andress7002/SeniorDesign/PCB Design/KiCad/CurrentSensing_DAUGHTERBOARD.kicad_sch

## KiCad design PCB Design/KiCad/CurrentSensing_DAUGHTERBOARD.kicad_sch (2026-03-03)

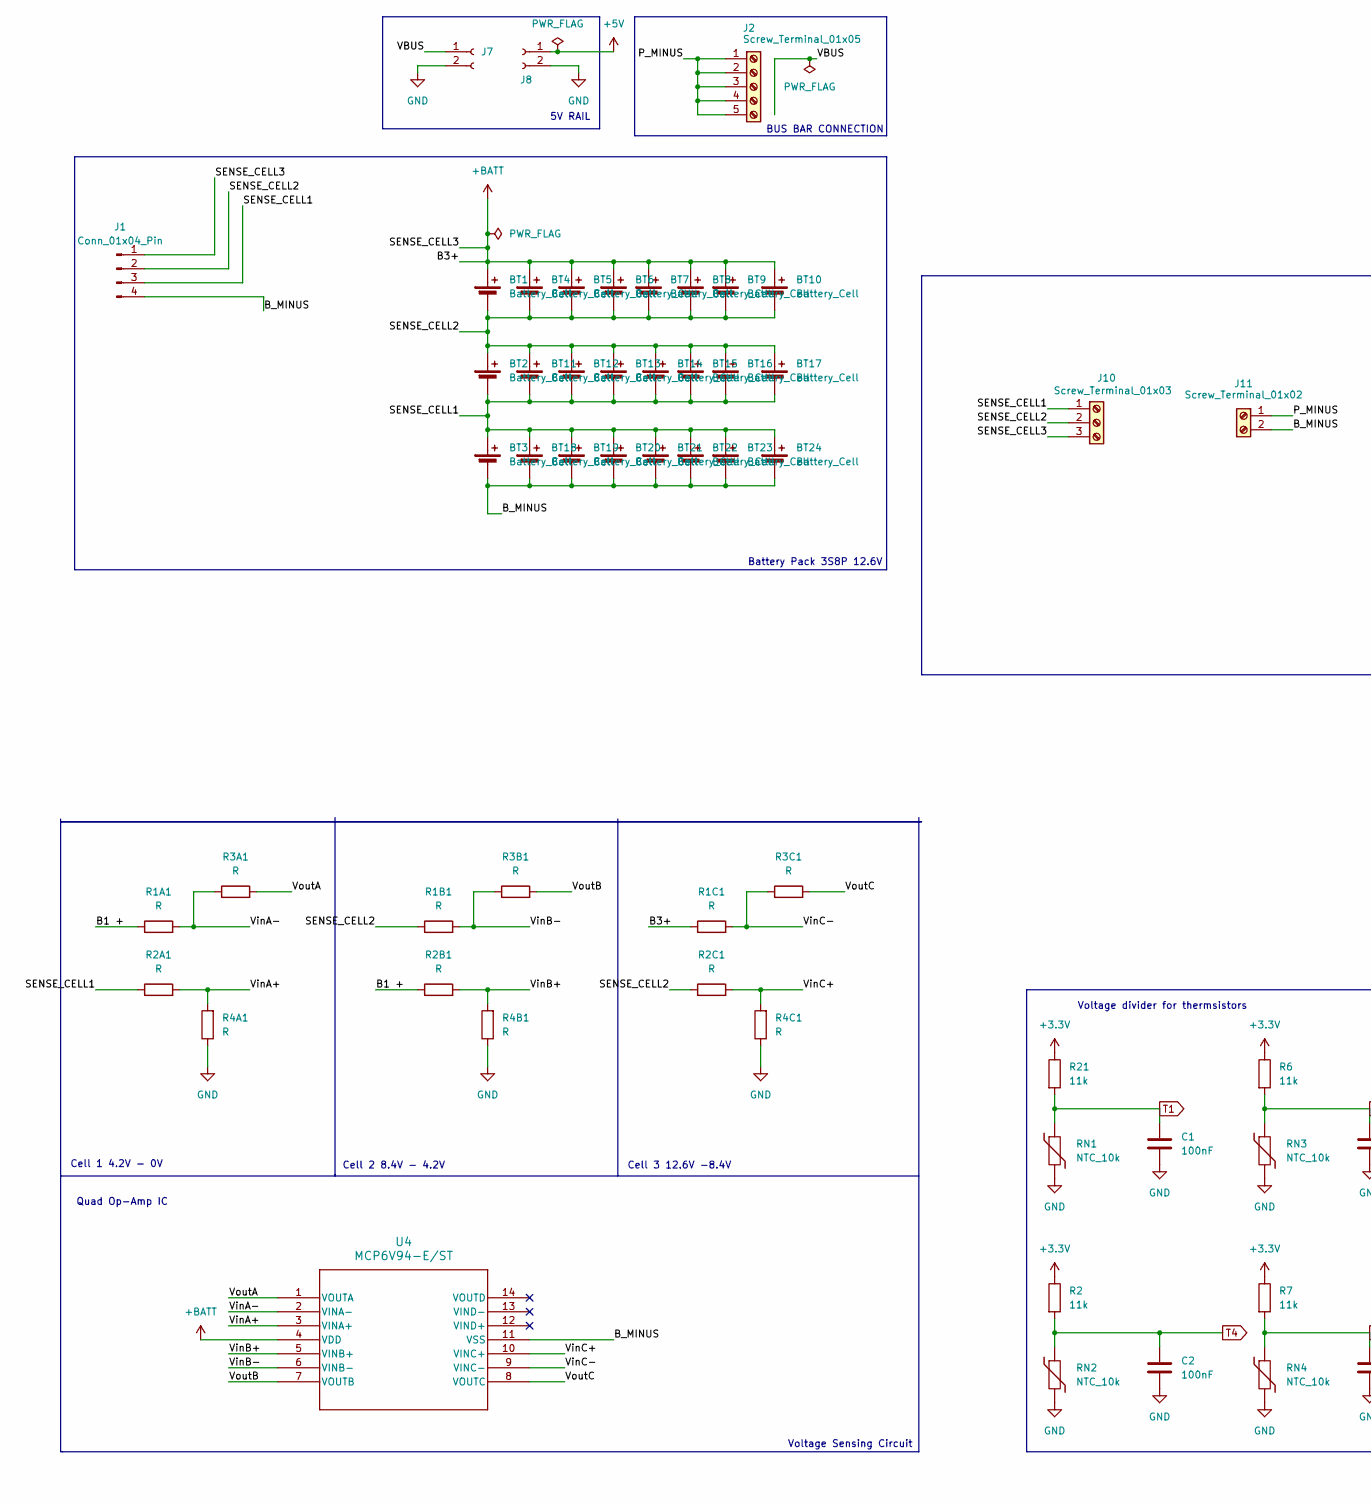
[picture p2: schematic CurrentSensing_DAUGHTERBOARD.kicad_sch, part in row 1, column 1]

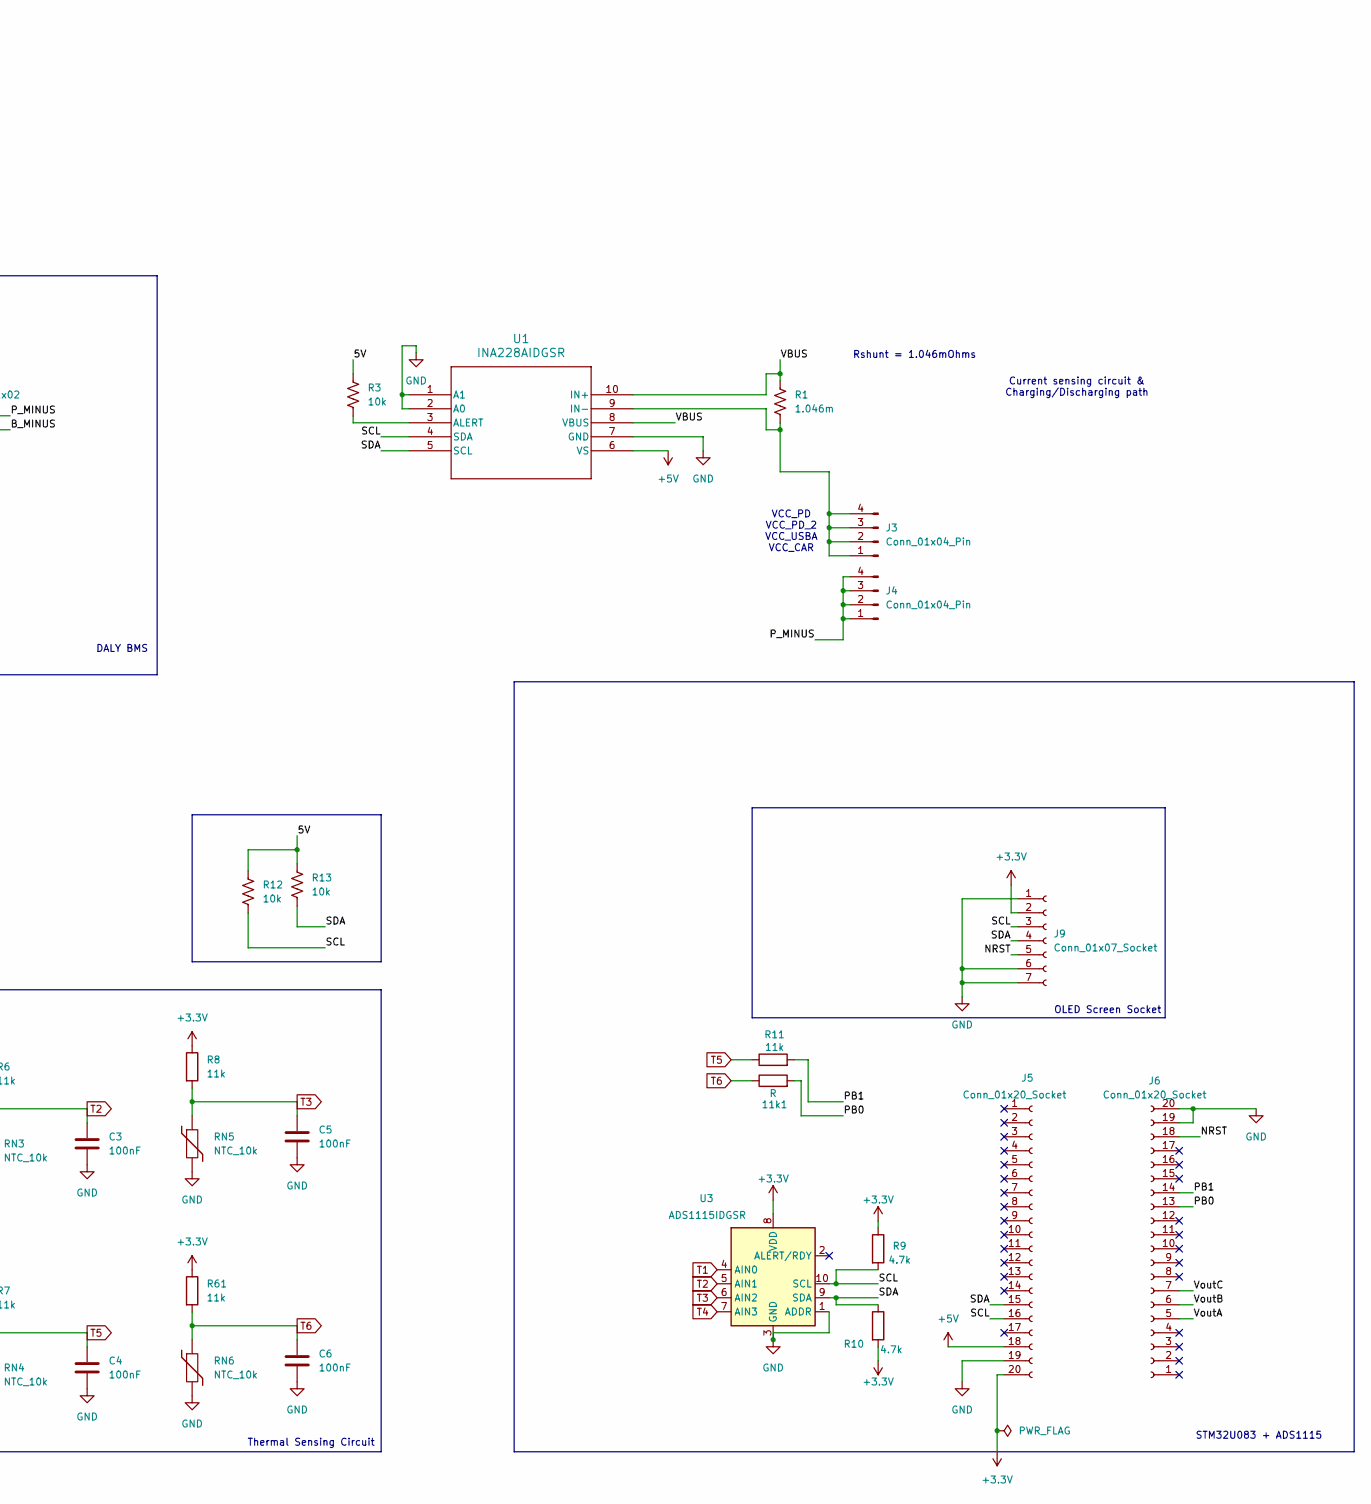
[picture p3: schematic CurrentSensing_DAUGHTERBOARD.kicad_sch, part in row 1, column 2]

Parts:
11k1: R
BT1, BT2, BT3, BT4, BT5, BT6, BT7, BT8, BT9, BT10, BT11, BT12, BT13, BT14, BT15, BT16, BT17, BT18, BT19, BT20, BT21, BT22, BT23, BT24: Battery_Cell
C1, C2, C3, C4, C5, C6: 100nF
J1, J3, J4: Conn_01x04_Pin
J2: Screw_Terminal_01x05
J5, J6: Conn_01x20_Socket
J7, J8: Conn_01x02_Socket
J9: Conn_01x07_Socket
J10: Screw_Terminal_01x03
J11: Screw_Terminal_01x02
R1: 1.046m
R1A1, R1B1, R1C1, R2A1, R2B1, R2C1, R3A1, R3B1, R3C1, R4A1, R4B1, R4C1: R
R2, R6, R7, R8, R11, R21, R61: 11k
R3, R12, R13: 10k
R9, R10: 4.7k
RN1, RN2, RN3, RN4, RN5, RN6: NTC_10k
U1: INA228AIDGSR; VSSOP10_DGS_TEX
U3: ADS1115IDGSR; MSOP-10_3x3mm_P0.5mm
U4: MCP6V94-E/ST; TSSOP14_ST_MCH

Connections:
5V: R3.1, R12.1, R13.1
+3.3V: J5.20, J9.2, R2.1, R6.1, R7.1, R8.1, R9.1, R10.2, R21.1, R61.1, U3.8 (VDD)
+5V: J5.18, J8.1, U1.6 (VS)
+BATT: BT1.1 (+), BT4.1 (+), BT5.1 (+), BT6.1 (+), BT7.1 (+), BT8.1 (+), BT9.1 (+), BT10.1 (+), J1.1, J10.3, R1C1.1, U4.4 (VDD)
B1 +: R1A1.1, R2B1.1
B_MINUS: BT3.2 (-), BT18.2 (-), BT19.2 (-), BT20.2 (-), BT21.2 (-), BT22.2 (-), BT23.2 (-), BT24.2 (-), J1.4, J11.2, U4.11 (VSS)
GND: C1.2, C2.2, C3.2, C4.2, C5.2, C6.2, J5.19, J6.19, J6.20, J7.2, J8.2, J9.1, J9.6, J9.7, R4A1.1, R4B1.1, R4C1.1, RN1.2, RN2.2, RN3.2, RN4.2, RN5.2, RN6.2, U1.1 (A1), U1.2 (A0), U1.7 (GND), U3.1 (ADDR), U3.3 (GND)
NRST: J6.18, J9.5
unnamed: J3.1, J3.2, J3.3, J3.4, R1.2, U1.9 (IN-)
unnamed: R3.2, U1.3 (ALERT)
PB0: 11k1.2, J6.13
PB1: J6.14, R11.2
P_MINUS: J2.1, J2.2, J2.3, J2.4, J2.5, J4.1, J4.2, J4.3, J4.4, J11.1
SCL: J5.16, J9.3, R9.2, R12.2, U1.4 (SDA), U3.10 (SCL)
SDA: J5.15, J9.4, R10.1, R13.2, U1.5 (SCL), U3.9 (SDA)
SENSE_CELL1: BT2.2 (-), BT3.1 (+), BT11.2 (-), BT12.2 (-), BT13.2 (-), BT14.2 (-), BT15.2 (-), BT16.2 (-), BT17.2 (-), BT18.1 (+), BT19.1 (+), BT20.1 (+), BT21.1 (+), BT22.1 (+), BT23.1 (+), BT24.1 (+), J1.3, J10.1, R2A1.1
SENSE_CELL2: BT1.2 (-), BT2.1 (+), BT4.2 (-), BT5.2 (-), BT6.2 (-), BT7.2 (-), BT8.2 (-), BT9.2 (-), BT10.2 (-), BT11.1 (+), BT12.1 (+), BT13.1 (+), BT14.1 (+), BT15.1 (+), BT16.1 (+), BT17.1 (+), J1.2, J10.2, R1B1.1, R2C1.1
T1: C1.1, R21.2, RN1.1, U3.4 (AIN0)
T2: C3.1, R6.2, RN3.1, U3.5 (AIN1)
T3: C5.1, R8.2, RN5.1, U3.6 (AIN2)
T4: C2.1, R2.2, RN2.1, U3.7 (AIN3)
T5: C4.1, R7.2, R11.1, RN4.1
T6: 11k1.1, C6.1, R61.2, RN6.1
VBUS: J7.1, R1.1, U1.8 (VBUS), U1.10 (IN+)
VinA+: R2A1.2, R4A1.2, U4.3 (VINA+)
VinA-: R1A1.2, R3A1.1, U4.2 (VINA-)
VinB+: R2B1.2, R4B1.2, U4.5 (VINB+)
VinB-: R1B1.2, R3B1.1, U4.6 (VINB-)
VinC+: R2C1.2, R4C1.2, U4.10 (VINC+)
VinC-: R1C1.2, R3C1.1, U4.9 (VINC-)
VoutA: J6.5, R3A1.2, U4.1 (VOUTA)
VoutB: J6.6, R3B1.2, U4.7 (VOUTB)
VoutC: J6.7, R3C1.2, U4.8 (VOUTC)

Notes on the sheet:
5V RAIL
Cell 3 12.6V -8.4V
Thermal Sensing Circuit
Rshunt = 1.046mOhms
Voltage divider for thermsistors
VCC_PD VCC_PD_2 VCC_USBA VCC_CAR
Battery Pack 3S8P 12.6V
Current sensing circuit & Charging/Discharging path
STM32U083 + ADS1115
Cell 1 4.2V - 0V
BUS BAR CONNECTION
Voltage Sensing Circuit
Quad Op-Amp IC
DALY BMS
Cell 2 8.4V - 4.2V
OLED Screen Socket
